ottoragam/Magnetic-Incremental-Rotary-Encoder/Pictures/parts.JPG

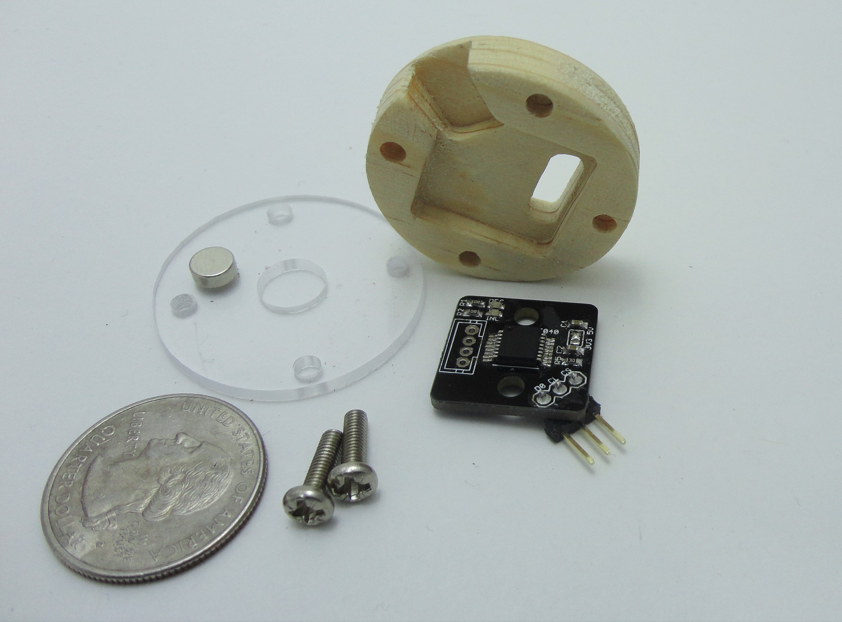
Pictures/parts.JPG
